flofuentesj/ECDL_LAMP/ICTP/poster_2.png

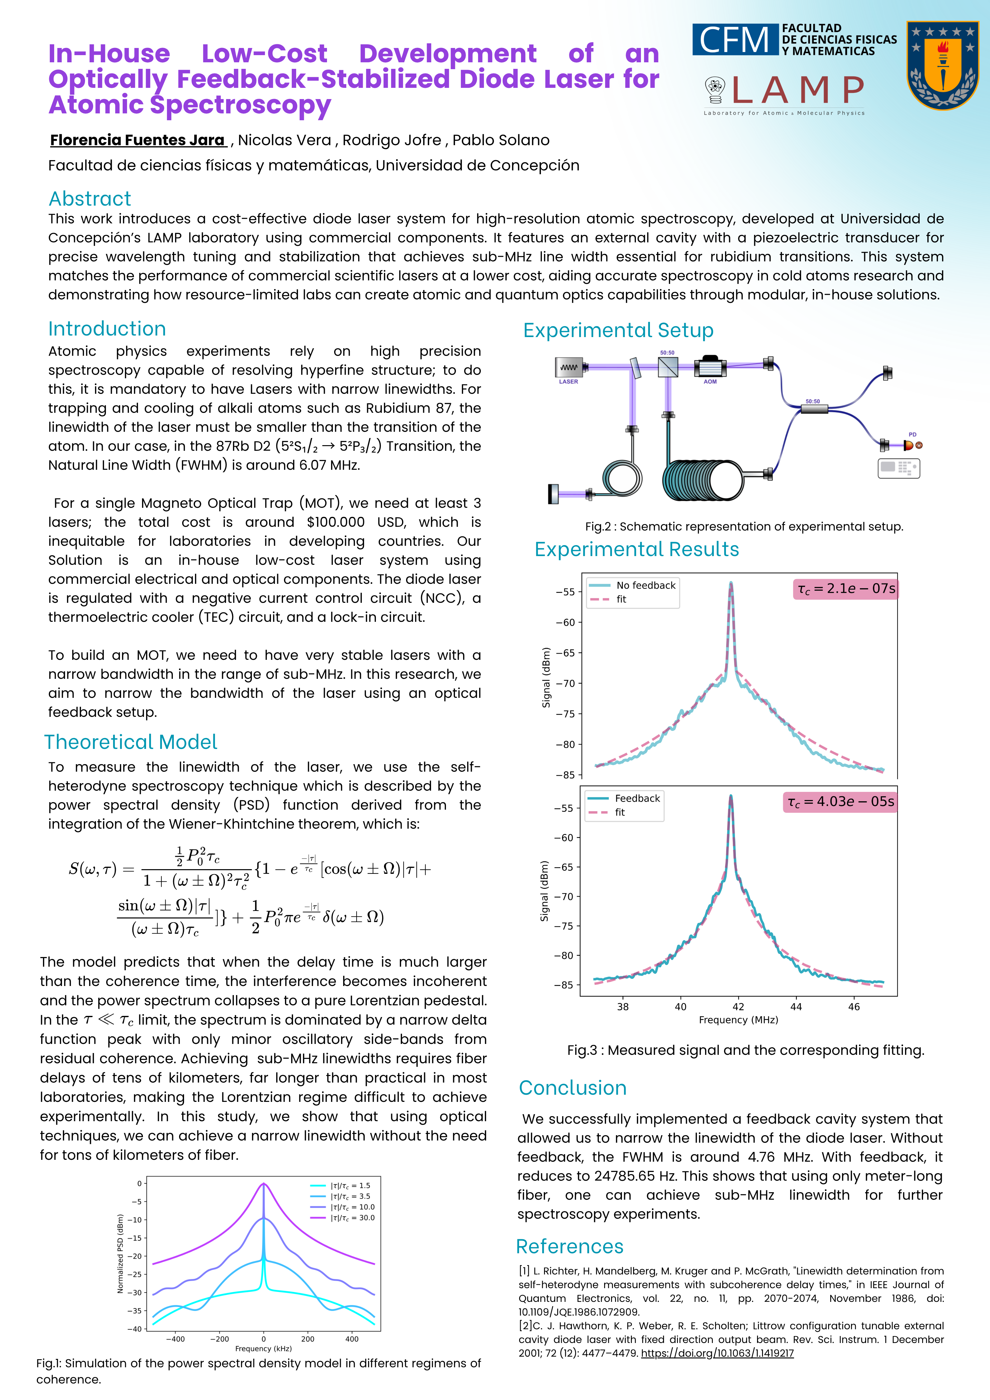
ICTP/poster_2.png
