flofuentesj/ECDL_LAMP/img/fitting_feedback_coherence_time.png

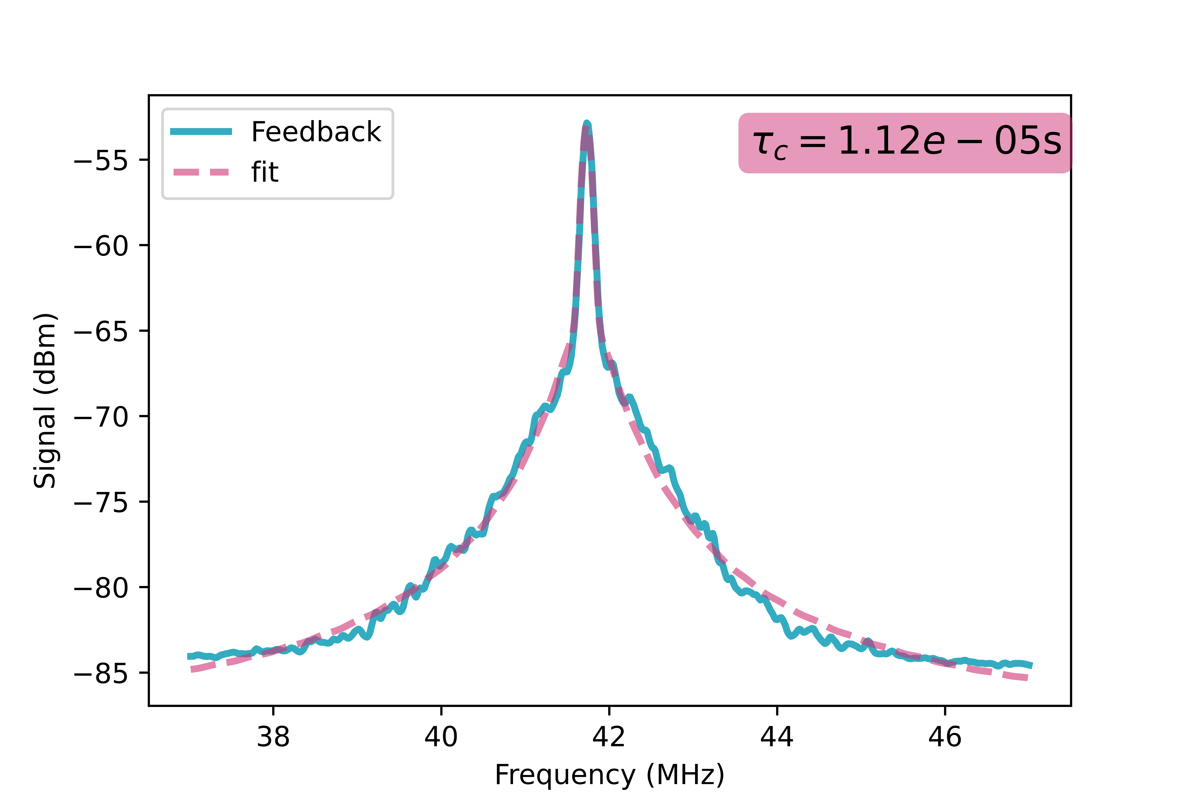
img/fitting_feedback_coherence_time.png
