flofuentesj/ECDL_LAMP/img/fitting_no_feedback_coherence_time.png

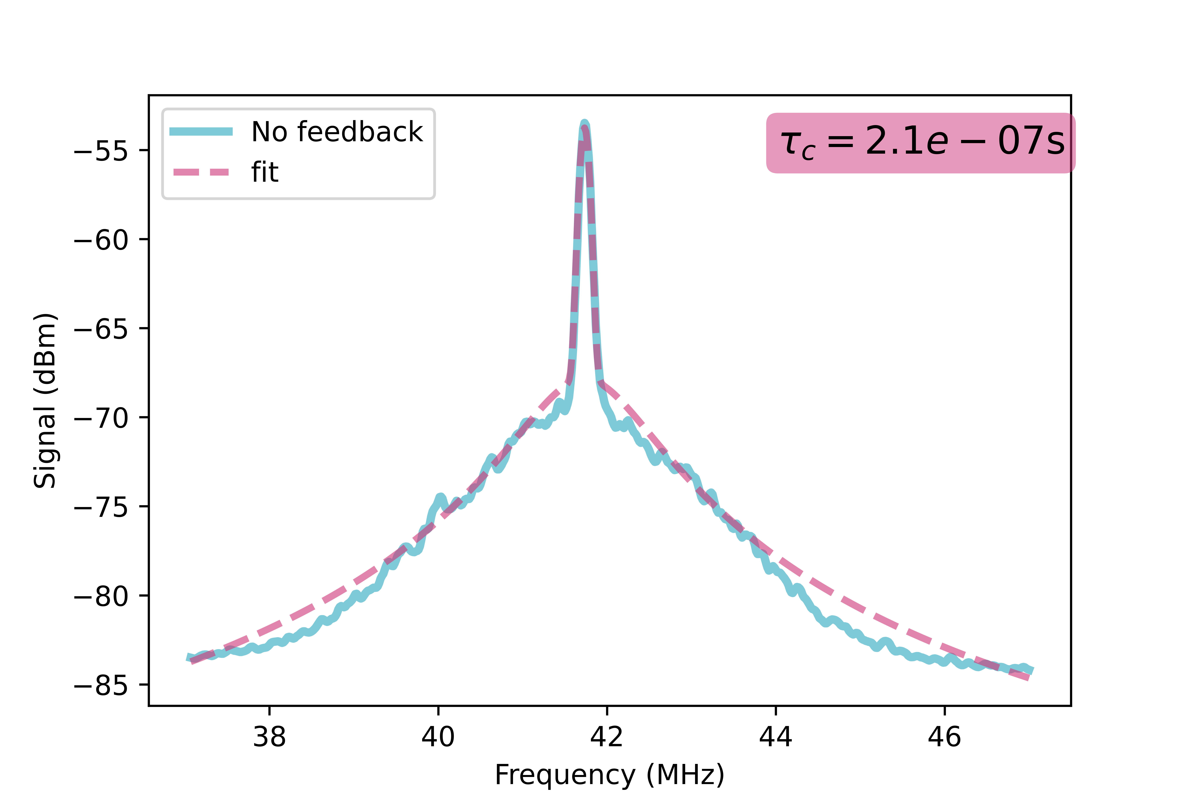
img/fitting_no_feedback_coherence_time.png
