flofuentesj/ECDL_LAMP/img/signal_vs_frequency.png

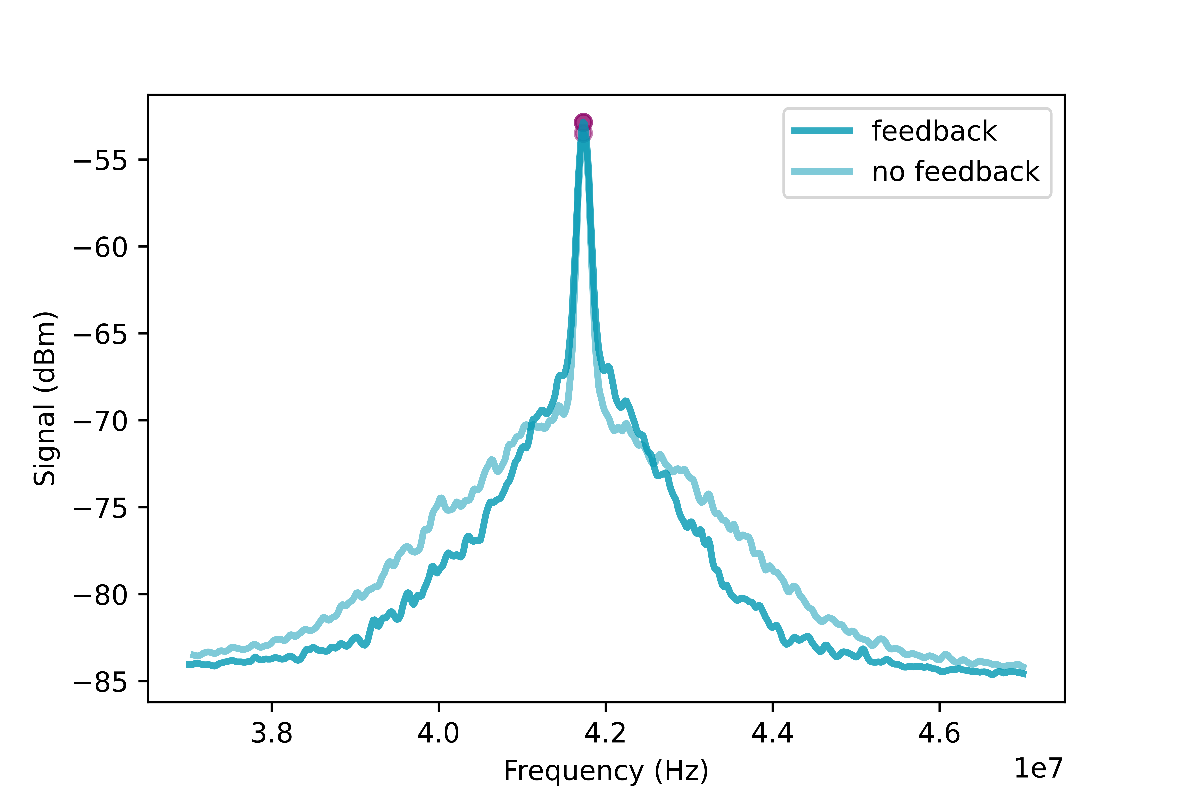
img/signal_vs_frequency.png
