flofuentesj/ECDL_LAMP/img/signalvsfrecuency.png

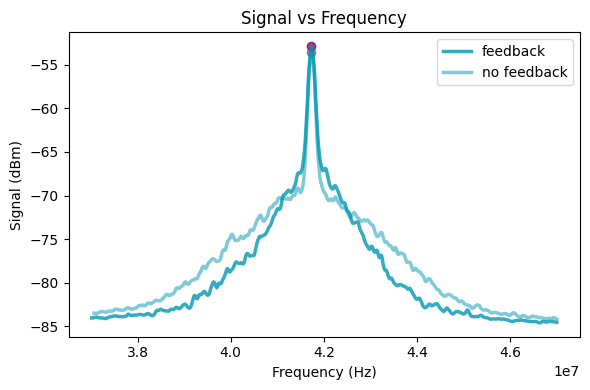
img/signalvsfrecuency.png
