flofuentesj/ECDL_LAMP/how_to_make_laser/images/experimental_setup.png

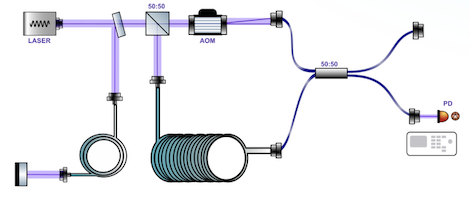
how_to_make_laser/images/experimental_setup.png
