flofuentesj/ECDL_LAMP/img/Setup.png

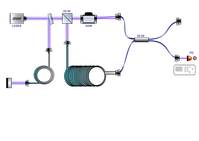
img/Setup.png
