flofuentesj/ECDL_LAMP/Circuits/piezo_controll_circuit.kicad_sch

## KiCad design Circuits/piezo_controll_circuit.kicad_sch (2026-07-18)

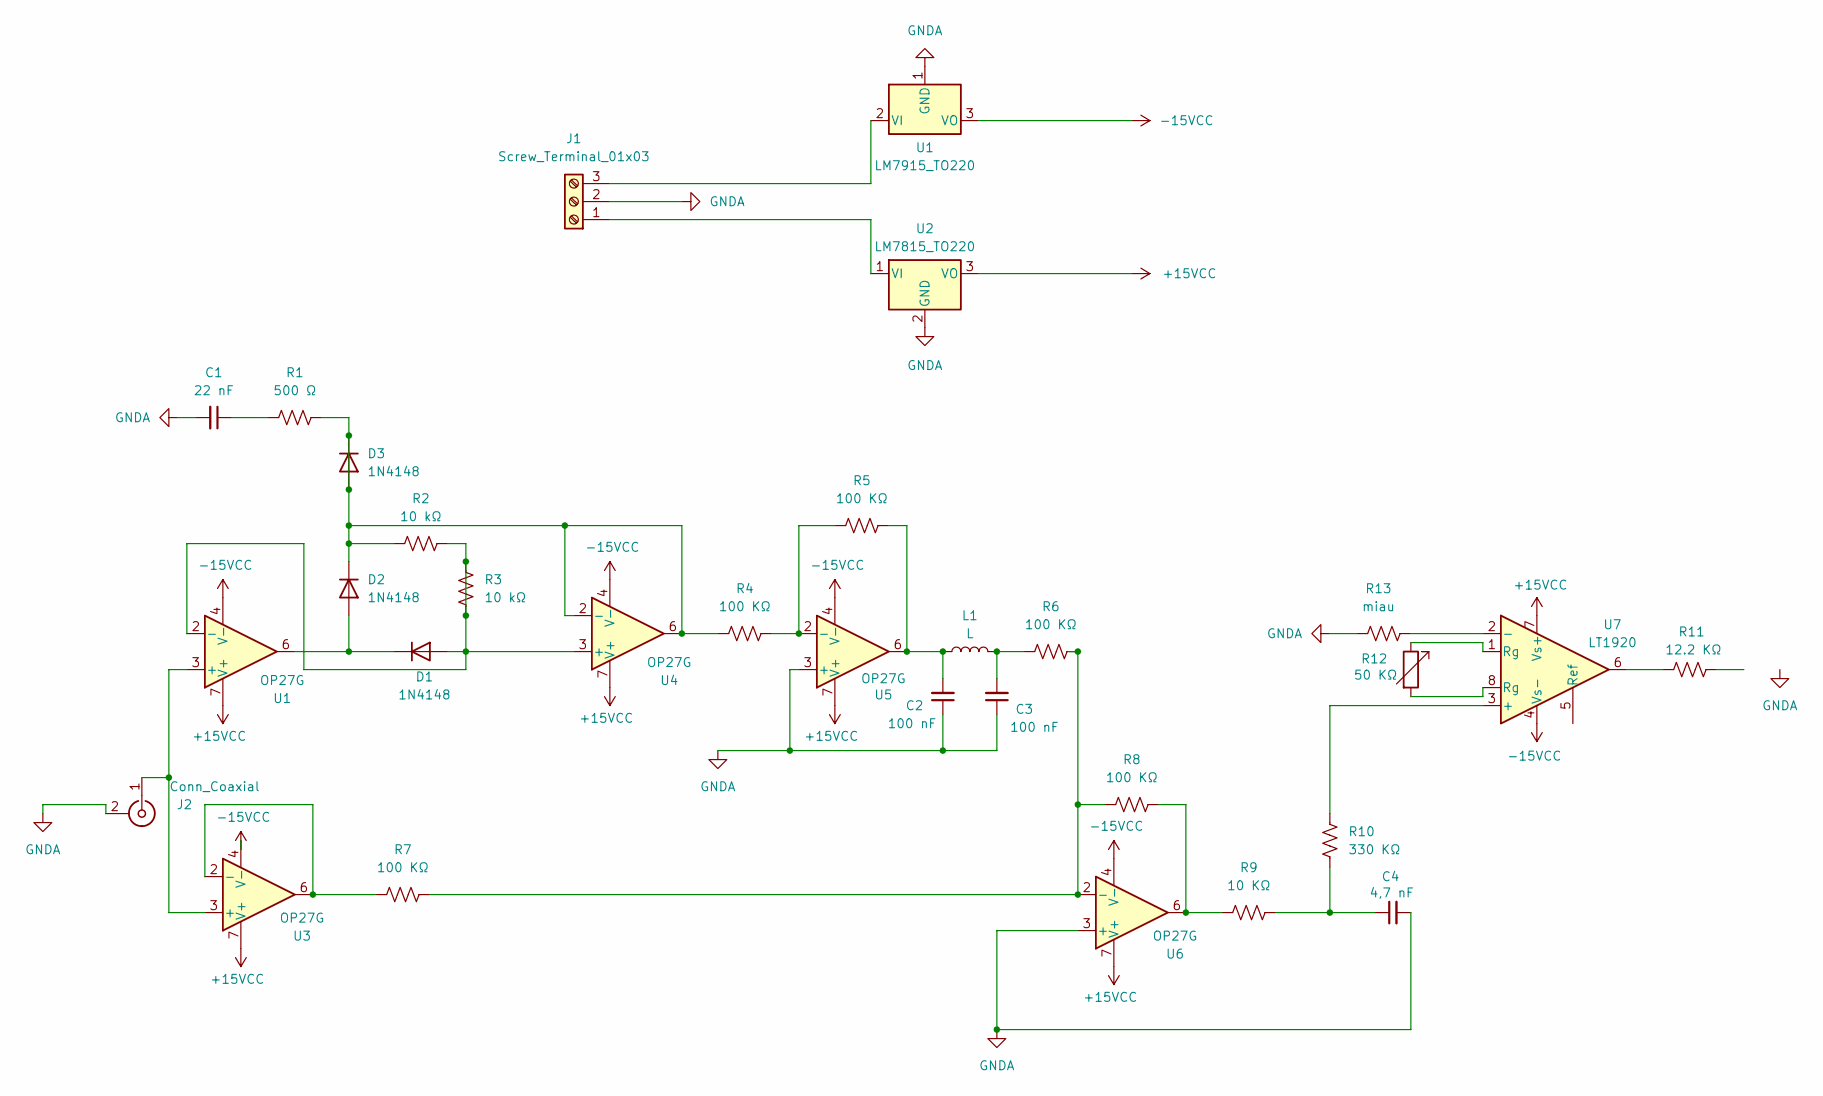
[picture p47: schematic piezo_controll_circuit.kicad_sch]

Parts:
C1: 22 nF; C_0201_0603Metric
C2, C3: 100 nF; C_0201_0603Metric
C4: 4,7 nF; C_0201_0603Metric
D1, D2, D3: 1N4148; D_SOD-523
J1: Screw_Terminal_01x03
J2: Conn_Coaxial
L1: L; L_6.3x6.3_H3
R1: 500 Ω; R_0201_0603Metric
R2, R3: 10 kΩ; R_0201_0603Metric
R4, R5, R6, R7, R8: 100 KΩ; R_0201_0603Metric
R9: 10 KΩ; R_0201_0603Metric
R10: 330 KΩ; R_0201_0603Metric
R11: 12.2 KΩ; R_0201_0603Metric
R12: 50 KΩ; R_0201_0603Metric
R13: miau; R_0201_0603Metric
U1, U3, U4, U5, U6: OP27G; DIP-8_W7.62mm
U2: LM7815_TO220; TO-220-3_Vertical
U7: LT1920; DIP-8_W7.62mm

Connections:
+15VCC: U1.7 (V+), U2.3 (VO), U3.7 (V+), U4.7 (V+), U5.7 (V+), U6.7 (V+), U7.7 (Vs+)
-15VCC: U1.3 (VO), U1.4 (V-), U3.4 (V-), U4.4 (V-), U5.4 (V-), U6.4 (V-), U7.4 (Vs-)
GNDA: C1.2, C2.1, C3.1, C4.2, J1.2, J2.2 (Ext), R13.1, U1.1 (GND), U2.2 (GND), U5.3 (+), U6.3 (+)
unnamed: C1.1, R1.2
unnamed: C2.2, L1.1, R5.2, U5.6
unnamed: C3.2, L1.2, R6.1
unnamed: C4.1, R9.2, R10.1
unnamed: D1.1 (K), D2.2 (A), U1.6
unnamed: D1.2 (A), R2.1, R3.1, R3.2, U1.2 (VI), U4.3 (+)
unnamed: D2.1 (K), D3.1 (K), D3.2 (A), R1.1, R2.2, R4.1, U4.2 (-), U4.6
unnamed: J1.1, U2.1 (VI)
unnamed: J1.3, U1.2 (VI)
unnamed: J2.1 (In), U1.3 (VO), U3.3 (+)
unnamed: R4.2, R5.1, U5.2 (-)
unnamed: R6.2, R7.2, R8.1, U6.2 (-)
unnamed: R7.1, U3.2 (-), U3.6
unnamed: R8.2, R9.1, U6.6
unnamed: R10.2, U7.3 (+)
unnamed: R11.1, U7.6
unnamed: R12.1, U7.1 (Rg)
unnamed: R12.2, U7.8 (Rg)
unnamed: R13.2, U7.2 (-)
